KoaCWells/BioCloneBot/CADs/Syringe Pump/TipEjectorBottomEnd.SLDPRT

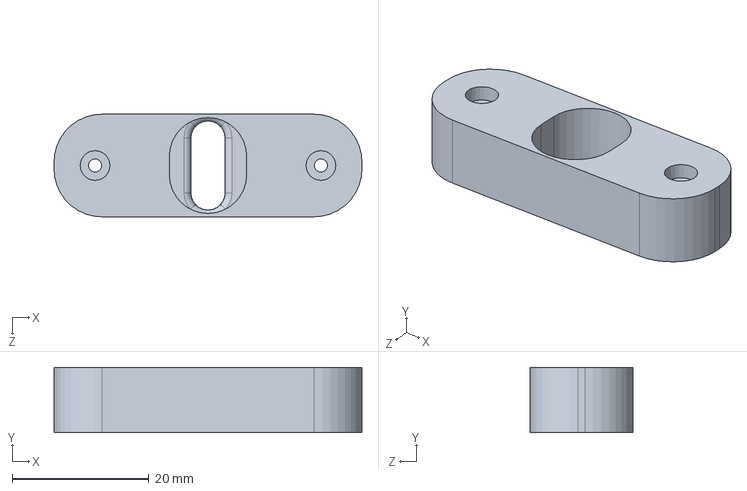
[picture p15: CAD file, 2023-02-14]
CADs/Syringe Pump/TipEjectorBottomEnd.SLDPRT
45.0 x 9.50 x 15.0 mm
