KoaCWells/BioCloneBot/CADs/Syringe Pump/TipEjectorTopEnd.SLDPRT

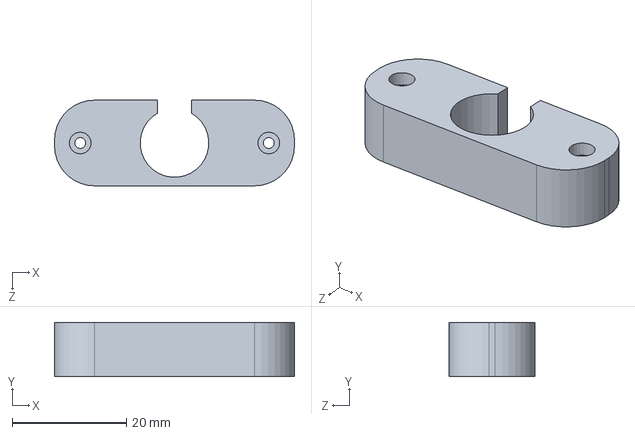
[picture p16: CAD file, 2023-02-14]
CADs/Syringe Pump/TipEjectorTopEnd.SLDPRT
42.0 x 9.50 x 15.0 mm
