KoaCWells/BioCloneBot/CADs/Syringe Pump/[MoonsSteppers]StepperMotor.step

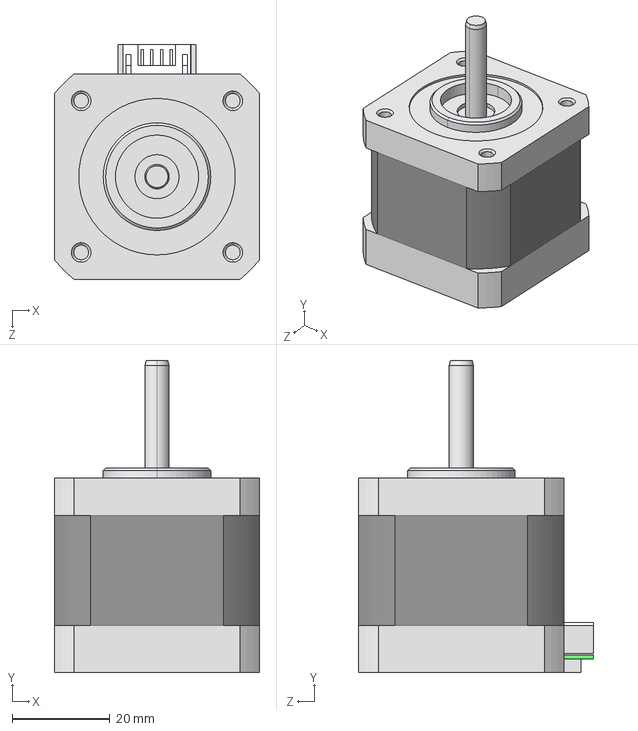
[picture p17: CAD file, 2023-02-11]
CADs/Syringe Pump/[MoonsSteppers]StepperMotor.step
42.0 x 63.8 x 48.0 mm
