KoaCWells/BioCloneBot/CADs/Syringe Pump/SyringeHolder.SLDPRT

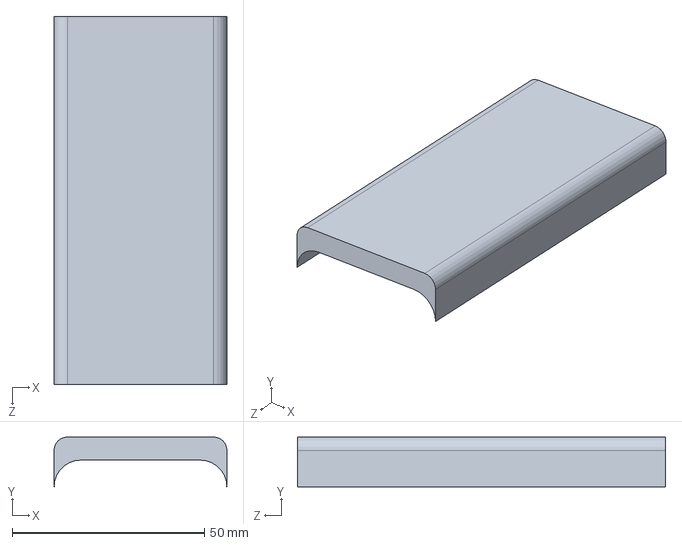
[picture p18: CAD file, 2023-02-11]
CADs/Syringe Pump/SyringeHolder.SLDPRT
45.0 x 13.0 x 95.8 mm
