KoaCWells/BioCloneBot/CADs/Syringe Pump/200uLTipAdapter.SLDPRT

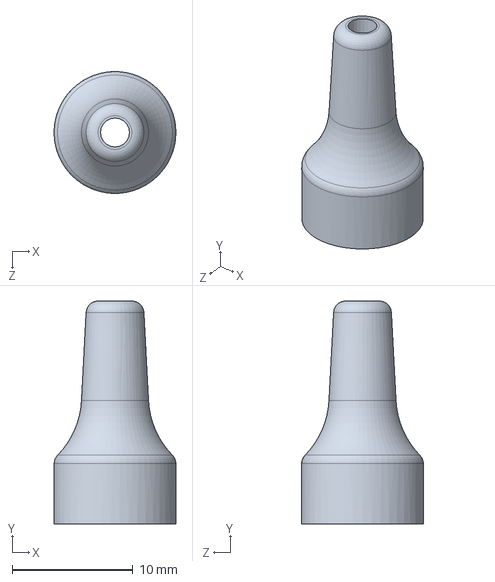
[picture p19: CAD file, 2023-02-11]
CADs/Syringe Pump/200uLTipAdapter.SLDPRT
10.1 x 18.5 x 10.1 mm
