KoaCWells/BioCloneBot/CADs/Syringe Pump/SyringePumpHolder.SLDPRT

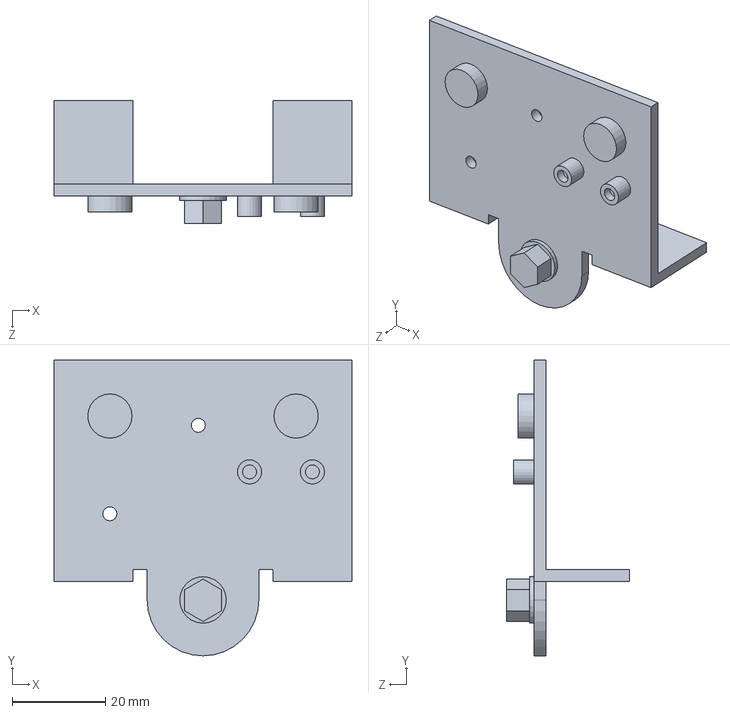
[picture p20: CAD file, 2023-02-11]
CADs/Syringe Pump/SyringePumpHolder.SLDPRT
64.0 x 63.5 x 26.5 mm
