KoaCWells/BioCloneBot/CADs/Syringe Pump/TipEjectorShaft.SLDPRT

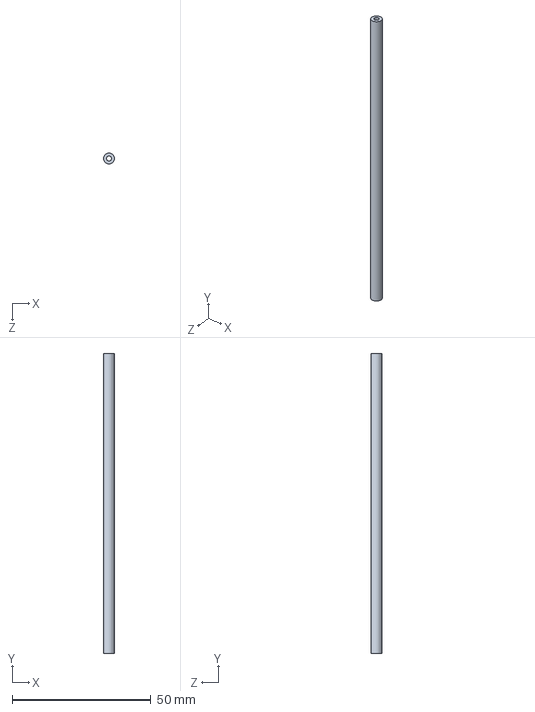
[picture p21: CAD file, 2023-02-11]
CADs/Syringe Pump/TipEjectorShaft.SLDPRT
3.90 x 108.0 x 3.90 mm
