KoaCWells/BioCloneBot/CADs/Syringe Pump/10uLTipAdapter.SLDPRT

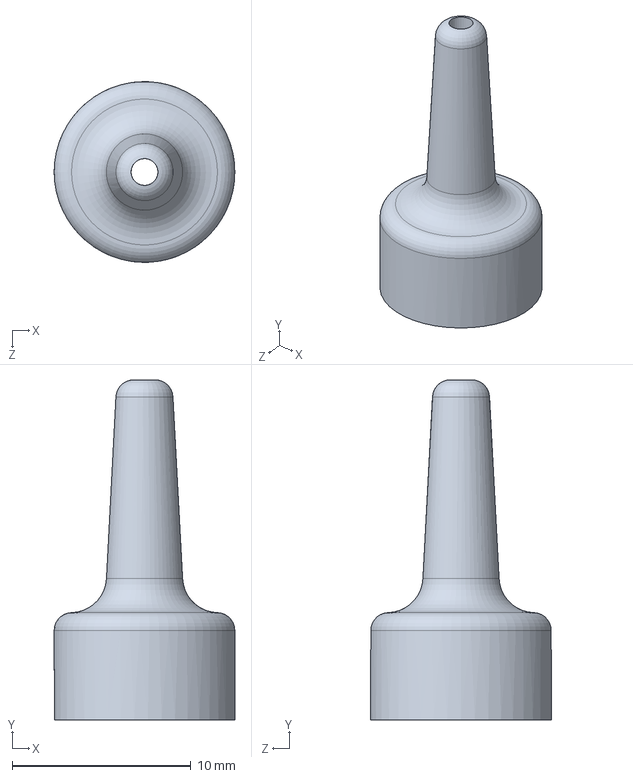
[picture p22: CAD file, 2023-02-11]
CADs/Syringe Pump/10uLTipAdapter.SLDPRT
10.1 x 19.0 x 10.1 mm
